huckley/kiwibad/sensors.h

#include <OneWire.h>
#include <DallasTemperature.h>

#define MAX_SENSORS 2
DeviceAddress air_sensor_addr[]   = {{ 0x28, 0xD7, 0xB9, 0xB3, 0x00, 0x00, 0x00, 0xFA },
                                     { 0x28, 0x6e, 0x85, 0x50, 0x00, 0x00, 0x00, 0x0f }};
DeviceAddress water_sensor_addr[] = {{ 0x28, 0xCE, 0xC8, 0x37, 0x00, 0x00, 0x00, 0x40 },
                                     { 0x28, 0xDC, 0x27, 0x38, 0x00, 0x00, 0x00, 0x5a }};

uint8_t getshortaddr(DeviceAddress addr) {
  uint8_t sum = 0;
  for (uint8_t i = 0; i < 8; i++) {
    sum += addr[i];
  }
  return sum;
}
