huckley/kiwibad/sender/Monospaced_bold_50.h

#ifdef ARDUINO
#include <Arduino.h>
#elif __MBED__
#define PROGMEM
#endif

// uint8_t not char
// Created by https://oleddisplay.squix.ch/ Consider a donation
// In case of problems make sure that you are using the font file with the correct version!
const uint8_t Monospaced_bold_50[] PROGMEM = {
  0x1E,  // Width: 30
  0x3B,  // Height: 59
  0x20,  // First Char: 32
  0xE0,  // Numbers of Chars: 224

  // Jump Table:
  0xFF, 0xFF, 0x00, 0x1E,  // 32:65535
  0x00, 0x00, 0x96, 0x1E,  // 33:0
  0x00, 0x96, 0xBC, 0x1E,  // 34:150
  0x01, 0x52, 0xEC, 0x1E,  // 35:338
  0x02, 0x3E, 0xD6, 0x1E,  // 36:574
  0x03, 0x14, 0xEE, 0x1E,  // 37:788
  0x04, 0x02, 0xEE, 0x1E,  // 38:1026
  0x04, 0xF0, 0x8C, 0x1E,  // 39:1264
  0x05, 0x7C, 0xAF, 0x1E,  // 40:1404
  0x06, 0x2B, 0xA5, 0x1E,  // 41:1579
  0x06, 0xD0, 0xD4, 0x1E,  // 42:1744
  0x07, 0xA4, 0xE5, 0x1E,  // 43:1956
  0x08, 0x89, 0x96, 0x1E,  // 44:2185
  0x09, 0x1F, 0xAD, 0x1E,  // 45:2335
  0x09, 0xCC, 0x96, 0x1E,  // 46:2508
  0x0A, 0x62, 0xD2, 0x1E,  // 47:2658
  0x0B, 0x34, 0xD5, 0x1E,  // 48:2868
  0x0C, 0x09, 0xDE, 0x1E,  // 49:3081
  0x0C, 0xE7, 0xCE, 0x1E,  // 50:3303
  0x0D, 0xB5, 0xD6, 0x1E,  // 51:3509
  0x0E, 0x8B, 0xD5, 0x1E,  // 52:3723
  0x0F, 0x60, 0xCD, 0x1E,  // 53:3936
  0x10, 0x2D, 0xD5, 0x1E,  // 54:4141
  0x11, 0x02, 0xCB, 0x1E,  // 55:4354
  0x11, 0xCD, 0xD6, 0x1E,  // 56:4557
  0x12, 0xA3, 0xD5, 0x1E,  // 57:4771
  0x13, 0x78, 0x96, 0x1E,  // 58:4984
  0x14, 0x0E, 0x96, 0x1E,  // 59:5134
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
};
